David2766/NAMO-aint-motion-only/components/radar_api_server/dashboard_handler.h

#pragma once

#include "esphome/components/web_server_base/web_server_base.h"

namespace esphome {
namespace radar_api_server {

class DashboardHandler {
 public:
  bool can_handle(AsyncWebServerRequest *request) const;
  bool handle(AsyncWebServerRequest *request) const;
};

}  // namespace radar_api_server
}  // namespace esphome
